stackOverHeap/feather-weather/source code/include/icons.h

#include "stdint.h"

uint64_t icon_temp64 = 0x000E11110A1A0A1E;
uint64_t icon_droplet64 = 0x000E1113110A0A04;

// uint64_t icon_PM64 = 0x11150A00101E110E;
// uint64_t icon_AM64 = 0x11150A00111F110E;

uint64_t icon_lowbat64 = 0x001F111111111B0E;
uint64_t icon_badrssi64 = 0x0004000A0400110E;
